BEKOS-Keyboards/Muse/3rd-party-footprints/RMCF0603FT100K/RMCF0603FT100K.step

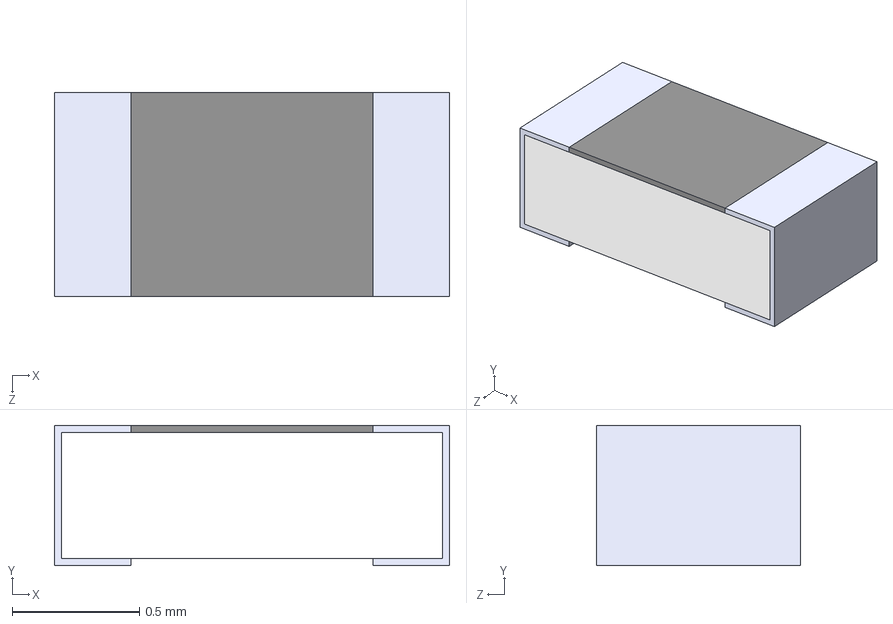
[picture p19: CAD file, 2020-12-28]
3rd-party-footprints/RMCF0603FT100K/RMCF0603FT100K.step
1.55 x 0.55 x 0.8 mm
