BEKOS-Keyboards/Muse/3rd-party-footprints/RMCF0805FT510R/RMCF0805FT510R.step

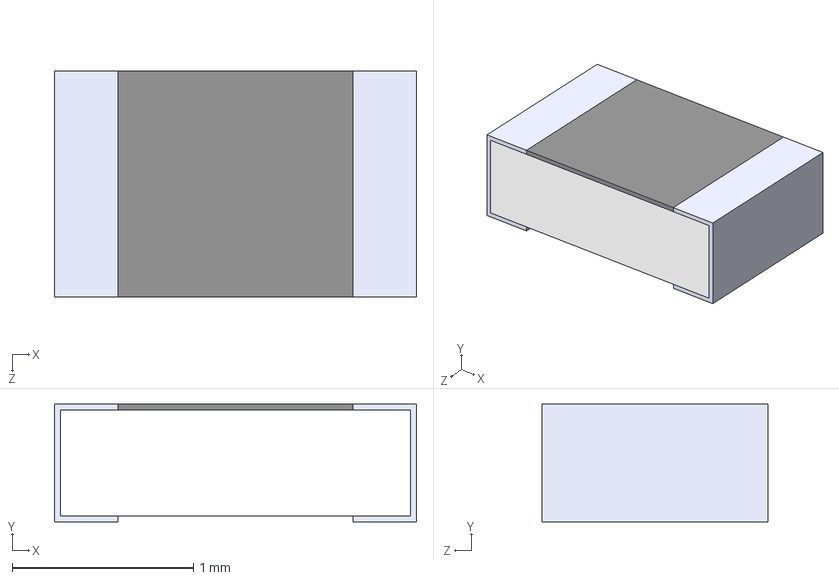
[picture p20: CAD file, 2020-12-31]
3rd-party-footprints/RMCF0805FT510R/RMCF0805FT510R.step
2.00 x 0.65 x 1.25 mm
