BEKOS-Keyboards/Muse/3rd-party-footprints/RMCF2512FT20K0/RMCF2512FT20K0.step

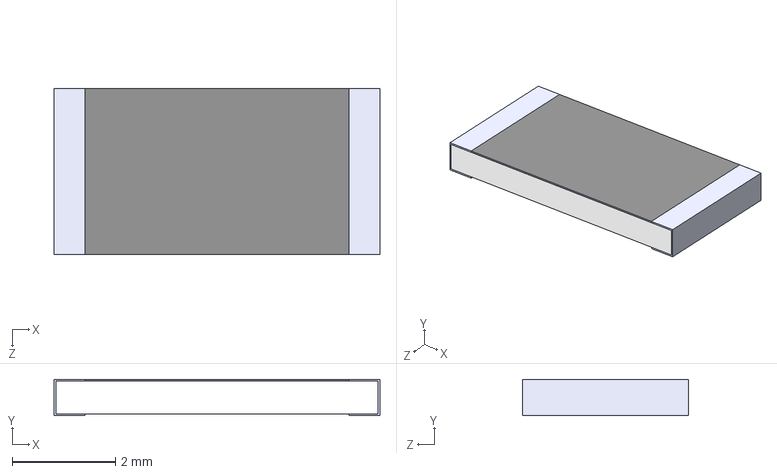
[picture p21: CAD file, 2020-12-28]
3rd-party-footprints/RMCF2512FT20K0/RMCF2512FT20K0.step
6.30 x 0.7 x 3.20 mm
