BEKOS-Keyboards/Muse/3rd-party-footprints/RNCP0603FTD10K0/RNCP0603FTD10K0.step

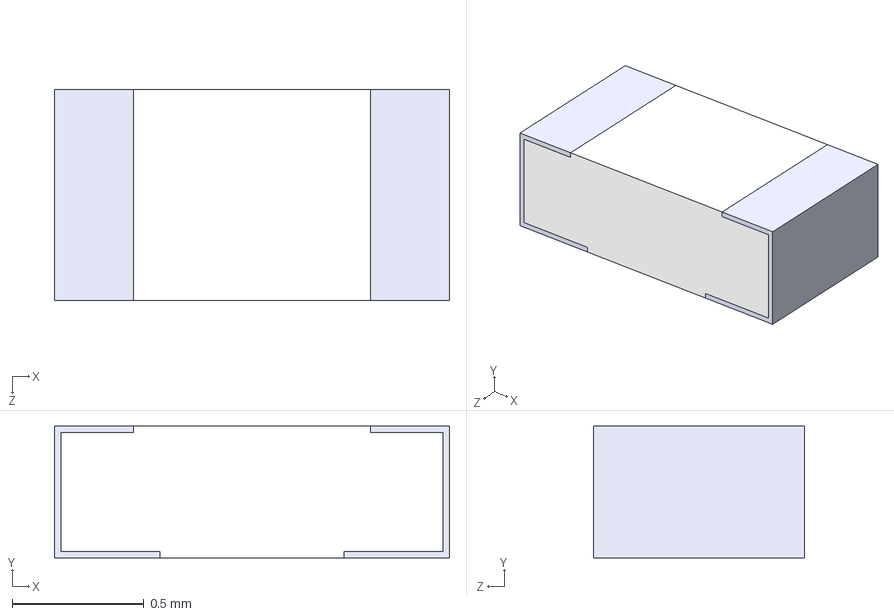
[picture p22: CAD file, 2020-12-28]
3rd-party-footprints/RNCP0603FTD10K0/RNCP0603FTD10K0.step
1.50 x 0.5 x 0.8 mm
