BEKOS-Keyboards/Muse/3rd-party-footprints/smd-quartz-3-2x2-5mm-1.snapshot.5/KX7 SMD Quartz Crystal Resonator 3.2x2.5mm.step

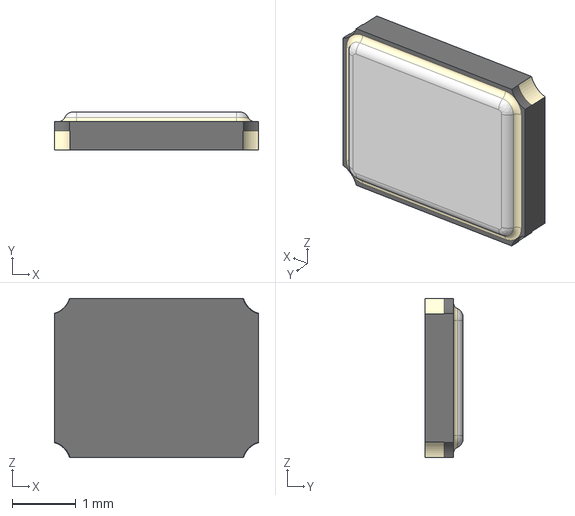
[picture p23: CAD file, 2021-02-27]
3rd-party-footprints/smd-quartz-3-2x2-5mm-1.snapshot.5/KX7 SMD Quartz Crystal Resonator 3.2x2.5mm.step
3.20 x 0.6 x 2.50 mm
