BEKOS-Keyboards/Muse/3rd-party-footprints/TAJB226K016RNJ/TAJB226K016RNJ.step

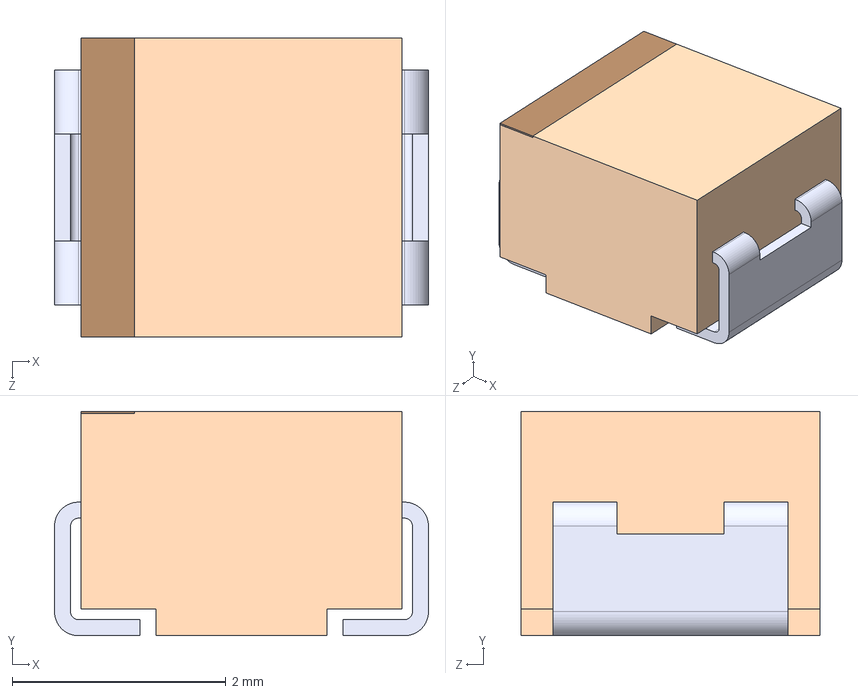
[picture p24: CAD file, 2020-12-28]
3rd-party-footprints/TAJB226K016RNJ/TAJB226K016RNJ.step
3.50 x 2.10 x 2.80 mm
