BEKOS-Keyboards/Muse/3rd-party-footprints/ul_SMAJ90CA/KiCAD/2021-01-04_17-23-41/STEP/SMASeries_LTF.step

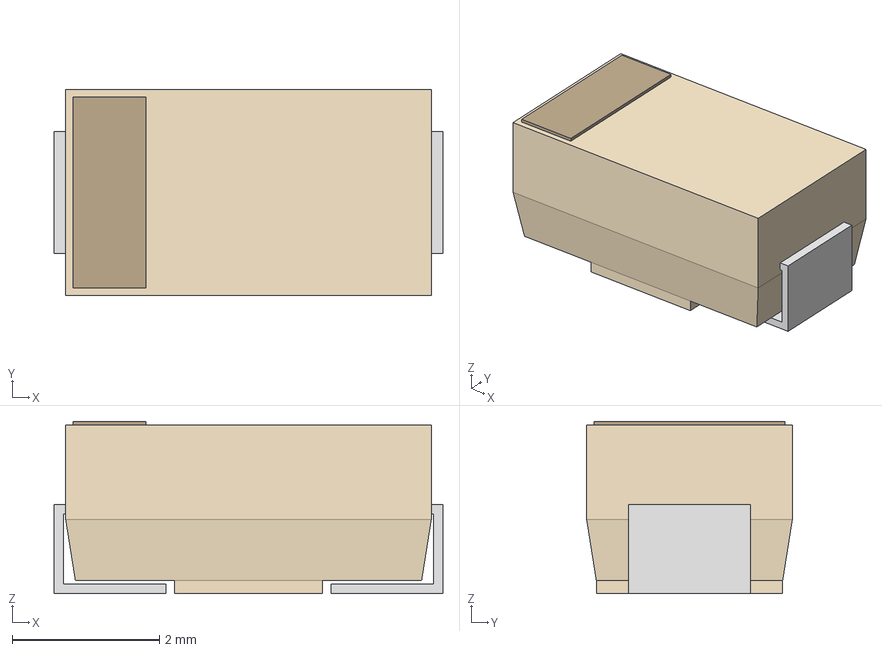
[picture p25: CAD file, 2021-01-04]
3rd-party-footprints/ul_SMAJ90CA/KiCAD/2021-01-04_17-23-41/STEP/SMASeries_LTF.step
5.28 x 2.79 x 2.34 mm
