BEKOS-Keyboards/Muse/3rd-party-footprints/USBLC6-2P6/USBLC6-2P6.step

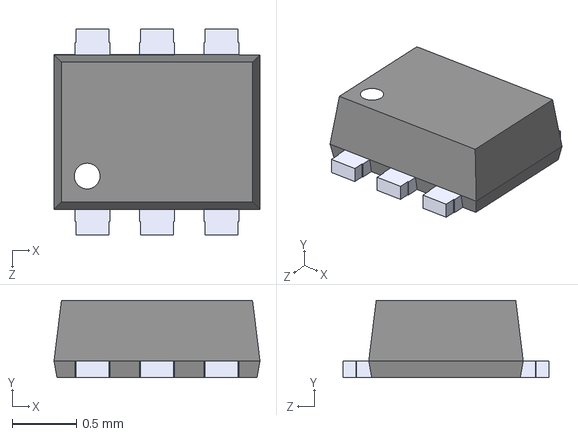
[picture p26: CAD file, 2020-12-31]
3rd-party-footprints/USBLC6-2P6/USBLC6-2P6.step
1.60 x 0.6 x 1.60 mm
