BEKOS-Keyboards/Muse/keyboard-layout/kb-plate-modded.dxf

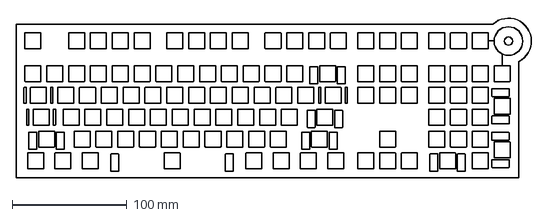
[picture p27: CAD file, 2020-12-30]
keyboard-layout/kb-plate-modded.dxf
449.9 x 140.5 mm
