BEKOS-Keyboards/Muse/3rd-party-footprints/19-337C_RSBHGHC-A88_4T.step

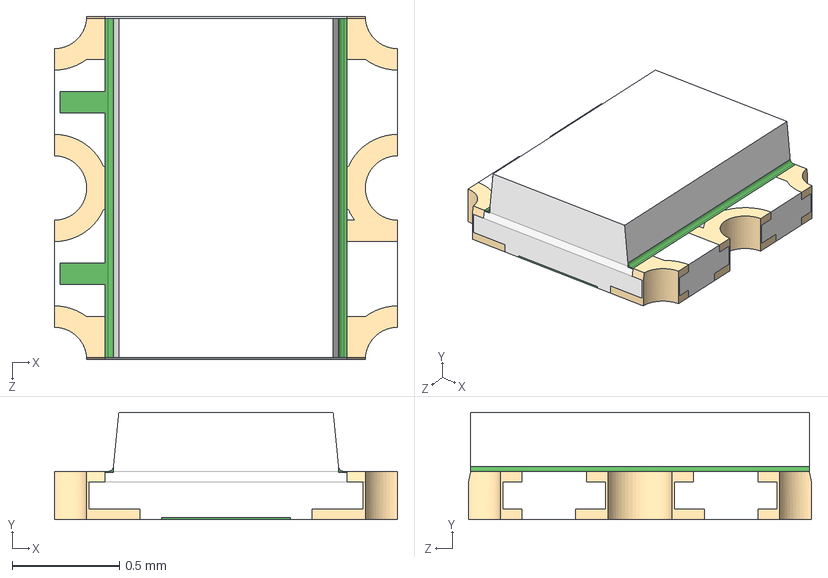
[picture p28: CAD file, 2020-12-27]
3rd-party-footprints/19-337C_RSBHGHC-A88_4T.step
1.60 x 0.5 x 1.60 mm
