BEKOS-Keyboards/Muse/keyboard-layout/kb-plate.dxf

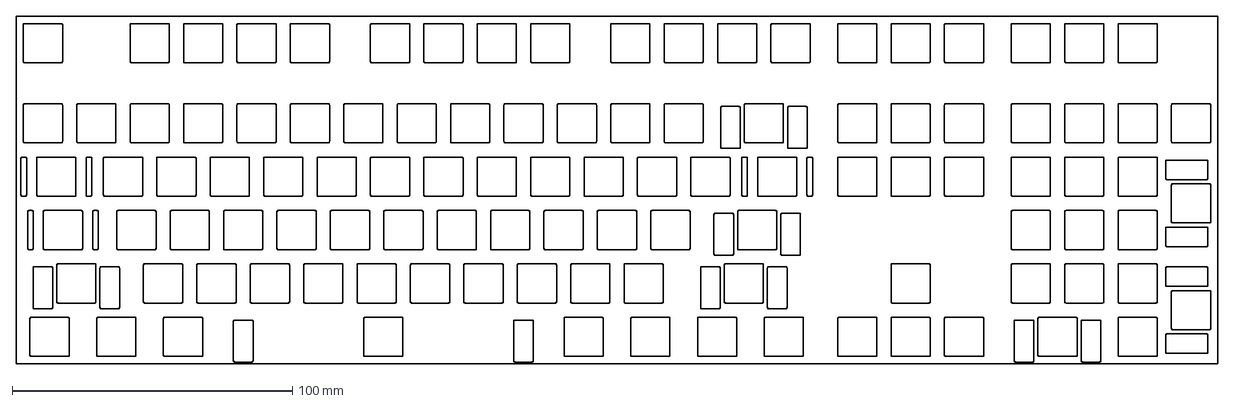
[picture p29: CAD file, 2020-12-30]
keyboard-layout/kb-plate.dxf
428.6 x 123.8 mm
